bitrot-alpha/lora-weather-esp32/src/receiver/include/lcd_chars.h

//our custom degree character
const uint8_t degree_char[] =
{
  0b00111,
  0b00101,
  0b00111,
  0b00000,
  0b00000,
  0b00000,
  0b00000,
  0b00000
};
const uint8_t deg_f_char[] =
{
  0b11100,
  0b10100,
  0b11100,
  0b00111,
  0b00100,
  0b00111,
  0b00100,
  0b00100
};
const uint8_t deg_c_char[] =
{
  0b11100,
  0b10100,
  0b11100,
  0b00000,
  0b00111,
  0b00100,
  0b00100,
  0b00111
};
const uint8_t in_char[] =
{
  0b00000,
  0b00000,
  0b10000,
  0b00111,
  0b10101,
  0b10101,
  0b10101,
  0b10101
};
const uint8_t hg_char[] =
{
  0b10100,
  0b11100,
  0b10100,
  0b00011,
  0b00101,
  0b00111,
  0b00001,
  0b00111
};
const uint8_t mm_char[] =
{
  0b00000,
  0b11110,
  0b10101,
  0b10101,
  0b00000,
  0b11110,
  0b10101,
  0b10101
};
const uint8_t hpa_char[] =
{
  0b10000,
  0b11100,
  0b10100,
  0b00000,
  0b11000,
  0b11010,
  0b10101,
  0b10011
};
